7B-Things/push-button-switch/pcb/push-button-switch/push-button-switch.kicad_sch

## KiCad design pcb/push-button-switch/push-button-switch.kicad_sch (2022-08-09)

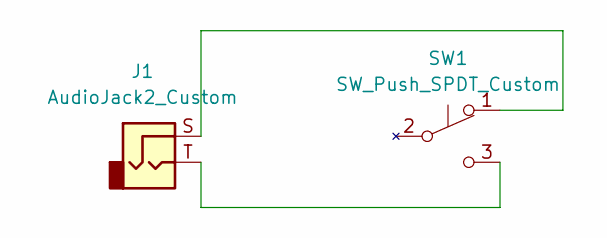
[picture p60: schematic push-button-switch.kicad_sch]

Parts:
J1: AudioJack2_Custom; 35RAPC2AHN2
SW1: SW_Push_SPDT_Custom; SPDT_Limit_Micro_Switch

Connections:
unnamed: J1.S, SW1.1 (A)
unnamed: J1.T, SW1.3 (C)
